jephilp/22RE_Igniter/Spice Models/IGF_Circuit.asc

C1: cap; 0.1µ; V=1K Irms=0 Rser=0.0165 Lser=1000p mfg="Würth Elektronik" pn="885342214173 WCAP-CSMH 2220" type="X7R"
C2: cap; 1µ; V=10 Irms=2.59 Rser=0.0171188 Lser=0 mfg="KEMET" pn="C0603C105K8RAC" type="X7R"
D1: diode; 1N4148
D2: diode; 1N4148
D3: zener; UFZV30B
D4: zener; UFZV30B
L1: ind; 1000n; Ipk=0.175 Rser=3.2 Rpar=25425.4 Cpar=0 mfg="Coilcraft" pn="0805CS-102"
Q1: npn; FZT849
Q2: npn; 2N2222
Q3: npn; 2N2222
Q4: npn; 2N2222
Q5: npn; 2N2222
R1: res; 6
R2: res; 10k
R3: res; 10k
R4: res; 2k
R5: res; 10k
R6: res; 10k
R7: res; 10k
R8: res; 390
R9: res; 10k
V1: voltage; 12
V2: signal; PULSE(0 5 0 1u 1u 50m 100m)
V3: voltage; 5
V4: voltage; 12
Named nets: 0
.tran 0 400m 0 100u
